makerstorage/GSM/firmware/web_auth/gsm_util.ino

int sim900_check_readable()
{
    return Serial.available();
}


void power_on(){

    uint8_t answer=0;
    
    // checks if the module is started
    answer = sendATcommand("AT", "OK", 2000);
    if (answer == 0)
    {
        // power on pulse
        digitalWrite(onModulePin,HIGH);
        delay(3000);
        digitalWrite(onModulePin,LOW);
    
        // waits for an answer from the module
        while(answer == 0){     // Send AT every two seconds and wait for the answer
            answer = sendATcommand("AT", "OK", 2000);    
        }
    }
    
}

int8_t sendATcommand(char* ATcommand, char* expected_answer, unsigned int timeout){

    uint8_t x=0,  answer=0;
    char response[100];
    unsigned long previous;

    memset(response, '\0', 100);    // Initialize the string

    delay(100);

    while( Serial.available() > 0) Serial.read();    // Clean the input buffer

    Serial.println(ATcommand);    // Send the AT command 


        x = 0;
    previous = millis();

    // this loop waits for the answer
    do{
        if(Serial.available() != 0){    
            // if there are data in the UART input buffer, reads it and checks for the asnwer
            response[x] = Serial.read();
            //Serial.print(response[x]);
            x++;
            // check if the desired answer  is in the response of the module
            if (strstr(response, expected_answer) != NULL)    
            {
                answer = 1;
            }
        }
    }
    // Waits for the asnwer with time out
    while((answer == 0) && ((millis() - previous) < timeout));    

        return answer;
}

int8_t sendATcommand2(char* ATcommand, char* expected_answer1, 
        char* expected_answer2, unsigned int timeout){

    uint8_t x=0,  answer=0;
    char response[100];
    unsigned long previous;

    memset(response, '\0', 100);    // Initialize the string

    delay(100);

    while( Serial.available() > 0) Serial.read();    // Clean the input buffer

    Serial.println(ATcommand);    // Send the AT command 

    x = 0;
    previous = millis();

    // this loop waits for the answer
    do{
        // if there are data in the UART input buffer, reads it and checks for the asnwer
        if(Serial.available() != 0){    
            response[x] = Serial.read();
            //Serial.print(response[x]);
            x++;
            // check if the desired answer 1  is in the response of the module
            if (strstr(response, expected_answer1) != NULL)    
            {
                answer = 1;
            }
            // check if the desired answer 2 is in the response of the module
            else if (strstr(response, expected_answer2) != NULL)    
            {
                answer = 2;
            }
        }
    }
    // Waits for the asnwer with time out
    while((answer == 0) && ((millis() - previous) < timeout));    

    return answer;
}

void sim900_clean_buffer(char *buffer, int count)
{
    for(int i=0; i < count; i++) {
        buffer[i] = '\0';
    }
}
 

void sim900_read_buffer(char *buffer, int count, unsigned int timeout, unsigned int chartimeout)
{
    int i = 0;
    unsigned long timerStart, prevChar;
    timerStart = millis();
    prevChar = 0;
    while(1) {
        while (sim900_check_readable()) {
            char c = Serial.read();
            prevChar = millis();
            buffer[i++] = c;
            if(i >= count)break;
        }
        if(i >= count)break;
        if ((unsigned long) (millis() - timerStart) > timeout * 1000UL) {
            break;
        }
        //If interchar Timeout => return FALSE. So we can return sooner from this function. Not DO it if we dont recieve at least one char (prevChar <> 0)
        if (((unsigned long) (millis() - prevChar) > chartimeout) && (prevChar != 0)) {
            break;
        }
    }
}
   
